machdyne/ferrit/fw/ferrit/src/mapper.h

#ifndef _MAPPER_H_
#define _MAPPER_H_

#include <stdint.h>

int mapper_luns(void);
int mapper_lun_size(uint8_t lun);
int mapper_rec(uint8_t lun, uint32_t addr);
int mapper_remaining(uint8_t lun, uint32_t addr);
uint32_t mapper_get_local_addr(uint8_t lun, uint32_t addr);
int mapper_get_drv(uint8_t lun, uint32_t addr);
int mapper_get_ss(uint8_t lun, uint32_t addr);
int mapper_get_cs(uint8_t lun, uint32_t addr);

#endif	// _MAPPER_H_
